olsson82/olshot/image/mainunit/IMG_3314.jpeg

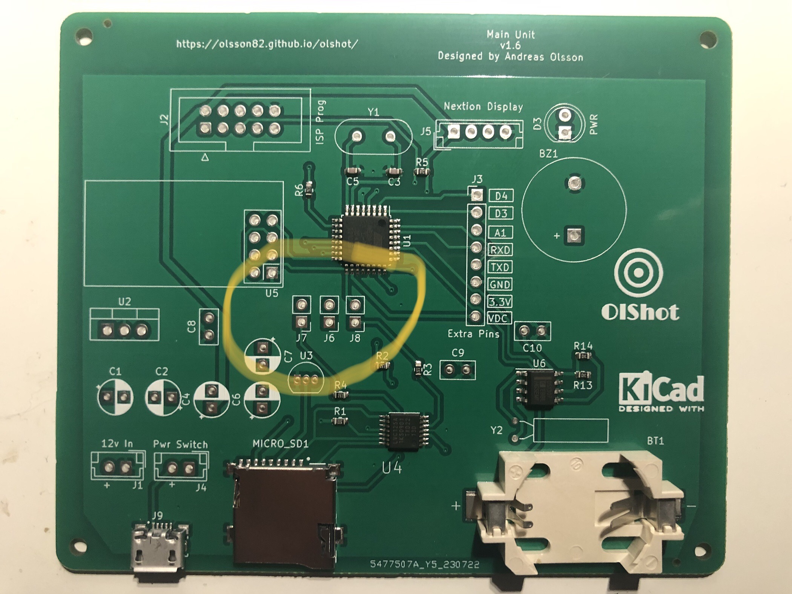
image/mainunit/IMG_3314.jpeg
