olsson82/olshot/image/target/shootingsensor_front.png

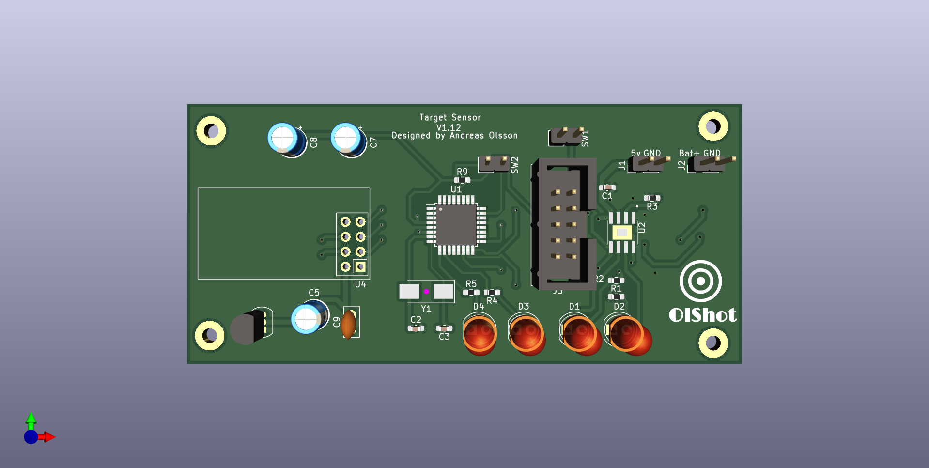
image/target/shootingsensor_front.png
